bierman/tos/src/raspi-os/pmod/led_matrix/font-6x8.c

// https://github.com/idispatch/raster-fonts/blob/master/font-6x8.c

#include "font.h"

#if 0
#ifndef FONT_H_
#define FONT_H_

typedef struct {
    unsigned char_width;
    unsigned char_height;
    const char * font_name;
    unsigned char first_char;
    unsigned char last_char;
    unsigned char * font_bitmap;
} font_t;

extern const font_t console_fonts[];

#endif /* FONT_H_ */
#endif
const unsigned char console_font_6x8[256 * 8] = {

    /*
     * code=0, hex=0x00, ascii="^@"
     */
    0x00,  /* 000000 */
    0x00,  /* 000000 */
    0x00,  /* 000000 */
    0x00,  /* 000000 */
    0x00,  /* 000000 */
    0x00,  /* 000000 */
    0x00,  /* 000000 */
    0x00,  /* 000000 */

    /*
     * code=1, hex=0x01, ascii="^A"
     */
    0x38,  /* 001110 */
    0x44,  /* 010001 */
    0x6C,  /* 011011 */
    0x44,  /* 010001 */
    0x54,  /* 010101 */
    0x44,  /* 010001 */
    0x38,  /* 001110 */
    0x00,  /* 000000 */

    /*
     * code=2, hex=0x02, ascii="^B"
     */
    0x38,  /* 001110 */
    0x7C,  /* 011111 */
    0x54,  /* 010101 */
    0x7C,  /* 011111 */
    0x44,  /* 010001 */
    0x7C,  /* 011111 */
    0x38,  /* 001110 */
    0x00,  /* 000000 */

    /*
     * code=3, hex=0x03, ascii="^C"
     */
    0x00,  /* 000000 */
    0x28,  /* 001010 */
    0x7C,  /* 011111 */
    0x7C,  /* 011111 */
    0x7C,  /* 011111 */
    0x38,  /* 001110 */
    0x10,  /* 000100 */
    0x00,  /* 000000 */

    /*
     * code=4, hex=0x04, ascii="^D"
     */
    0x00,  /* 000000 */
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
    0x00,  /* 000000 */
    0x00,  /* 000000 */

    /*
     * code=255, hex=0xFF, ascii="!^�"
     */
    0x00,  /* 000000 */
    0x00,  /* 000000 */
    0x00,  /* 000000 */
    0x00,  /* 000000 */
    0x00,  /* 000000 */
    0x00,  /* 000000 */
    0x00,  /* 000000 */
    0x00,  /* 000000 */
};
